sskonda/CANSAT-Telemetry-Team/Sensors_Combined_Code/altitude_blueprint.py

#"getPressure" and "getTemp" function not implemented,
#but should return the pressure (as Pa) and temp (as *K) as floats
def getPressure():
    return 100000

def getTemp():
    return 300.0

#method 1: statistical approximation (Pa, *k)
def approxAlt(pressure, temp)
    #input pressure as Pa
    sea_press = 101325
    #approximate barometic pressure at sea level (Pa)
    #Note!!! this should draw from a regularly updated database or this will cause big difference
    return (pow((sea_press / pressure), 0.1903) -1)*(temp)/0.0065
    #this one assumes no change in T vs H


#method 2: calibrated altitude difference measuring (Pa, m, *k)
#measure a pressure at ground level and record the altitude at ground level
#perhaps use the approximation function for an inital height?
#p0 = initial pressure, h0 = initial height
#p = most recent pressure reading, t0 = temperature at starting height
def altDifference(p0, p, h0, t0):
    a = .0065 #approximate temperature lapse rate 0-1000m (*k/m)
    
    return(t0/a)*pow(1-(p/p0),.190294)
    #interestingly, because temperature varies (roughly) linearly with height up to ~2000m, a second temperature
    #measurement isn't super necessary

#flow of operation:
def main():
    start_press = getPressure()
    start_temp = getTemp()
    sea_press = 101325  #Note!!! this should draw from a regularly updated database or this will cause big difference
    start_height = altDifference(sea_press, start_press, 0, start_temp)
    #...
    while(flying):
        height1 = start_height + altDifference(start_press, getPressure(), start_height, start_temp)
        #or:
        height2 = approxAlt(getPressure(), start_temp)
    
